mjamiv/SiteEye/case-design/molt-v2-back.stl

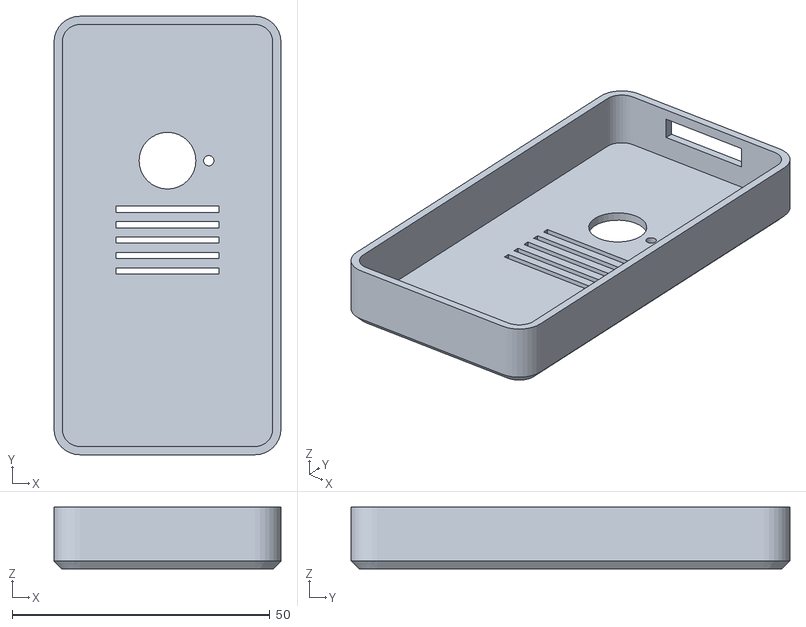
[picture p25: CAD file, 2026-03-21, an earlier design]
case-design/molt-v2-back.stl
44.0 x 85.0 x 12.0
